eskyh/OilSense/myLibs/sensors/sensor.cpp

#include "sensor.hpp"

// name: sensor name
// nMeasures: number of measures a sensor can generator (some sensor integrates multiple type of measures)
Sensor::Sensor(const char *sensorName, int nMeasures,
               FilterType filter,
               BandType band, uint16_t gap, bool pct)
{
    // sizeof: Returns the length of the given byte string, include null terminator;
    // strlen: Returns the length of the given byte string not including null terminator;
    strncpy(name, sensorName, sizeof(name));
    _nMeasures = nMeasures;

    // init the filter pointer array
    _filters = new Filter *[_nMeasures];
    for (int i = 0; i < _nMeasures; i++)
    {
        _filters[i] = NULL;
    }

    setFilter(filter);

    // init the band pointer array
    _bands = new Band *[_nMeasures];
    for (int i = 0; i < _nMeasures; i++)
    {
        _bands[i] = NULL;
    }

    setBand(band, gap, pct);

    // init the measure array
    _measures = (float *)calloc(nMeasures, sizeof(float));
}

Sensor::~Sensor()
{
    for (int i = 0; i < _nMeasures; i++)
    {
        if (_filters[i] != NULL)
            delete _filters[i];
    }

    free(_measures);
}

void Sensor::setFilter(FilterType type)
{
    for (int i = 0; i < _nMeasures; i++)
    {
        setFilter(i, type);
    }
}

void Sensor::setFilter(int index, FilterType type)
{
    if (_filters[index] != NULL)
    {
        delete _filters[index];
        _filters[index] = NULL;
    }

    switch (type)
    {
    case FT_None:
        _filters[index] = NULL;
        break;
    case Median:
        _filters[index] = new MedianFilter();
        break;
    case Kalmen:
        _filters[index] = new KalmenFilter();
        break;
    case EWMA:
        _filters[index] = new EWMAFilter();
        break;
    }
}

void Sensor::setBand(BandType type, uint16_t gap, bool pct)
{
    for (int i = 0; i < _nMeasures; i++)
    {
        setBand(i, type, gap, pct);
    }
}

void Sensor::setBand(int index, BandType type, uint16_t gap, bool pct)
{
    if (_bands[index] == NULL)
        _bands[index] = new Band();
    _bands[index]->reset(type, gap, pct);

    // if(type == BandType::None)
    // {
    // 	if(_bands[index] != NULL)
    // 	{
    // 		delete _bands[index];
    // 		_bands[index] = NULL;
    // 	}
    // }else
    // {
    // 	if(_bands[index] == NULL)	_bands[index] = new Band();
    // 	_bands[index]->reset(type, gap, pct);
    // }
}

// qos :
//     0: At most once
//     1: At least once
//     2: Exactly once
void Sensor::setMqtt(AsyncMqttClient *pClient, const char *topic, int qos, bool retain)
{
    _pMqttClient = pClient;

    // write the default topic of the sensor for mqtt
    // strcpy(_topic, topic);
    strncpy(_topic, topic, sizeof(_topic));

    _qos = qos;
    _retain = retain;
}

// Send MQTT measurement message to MQTT broker!
void Sensor::sendMeasure()
{
    // do not do anything if disabled or not connected to network
    if (!_enabled || _pMqttClient == NULL || !_pMqttClient->connected())
        return;

    // Accuracy only to 1mm. so output to 1 decimal place.
    if (!measure())
    {
        Serial.printf("%s: measure failed!\n", name);
        return;
    }

    char *payload = getPayload();
    if (payload == NULL)
        return;

    _pMqttClient->publish(_topic, _qos, _retain, payload); // retain will clear the chart when deploying!! set it to false

#ifdef _DEBUG
    Serial.printf("%s: %s\n", _topic, payload); // name, _topic, payload);
#endif
}

// Perform measurement (unit: cm)
bool Sensor::measure()
{
    if (!_enabled || !_read())
        return false;

    _timestamp = time(NULL); // get current timestamp

    for (int i = 0; i < _nMeasures; i++)
    {
        // Get the filtered value if a filter is set.
        if (_filters[i] != NULL)
            _measures[i] = _filters[i]->state(_measures[i]);

        _bands[i]->check(_measures[i]);
    }

    return true;
}
