eskyh/OilSense/myLibs/sensors/dht11.hpp

#pragma once

#include "sensor.hpp"
#include "DHT.h"

/*
 * DH11 temperature / humidity sensor class
 */
class DH11 : public Sensor
{
public:
    DH11(const char *name, uint8_t dhtPin);
    virtual char *getPayload();

private:
    DHT _dht;

    virtual bool _read();
};
